ryomuk/tangnano-MCS4memory/src/TangNanoMCS4_project/src/gowin_rpll/gowin_rpll_tmp.v

//Copyright (C)2014-2023 Gowin Semiconductor Corporation.
//All rights reserved.
//File Title: Template file for instantiation
//GOWIN Version: V1.9.8.11 Education
//Part Number: GW2AR-LV18QN88C8/I7
//Device: GW2AR-18
//Device Version: C
//Created Time: Fri Jun 02 09:45:17 2023

//Change the instance name and port connections to the signal names
//--------Copy here to design--------

    Gowin_rPLL your_instance_name(
        .clkout(clkout_o), //output clkout
        .clkin(clkin_i) //input clkin
    );

//--------Copy end-------------------
